ProjectAVR/minDUINO-v1.6-Eagle-/minDUINO v1.6_Gerblook_FRONT.jpg

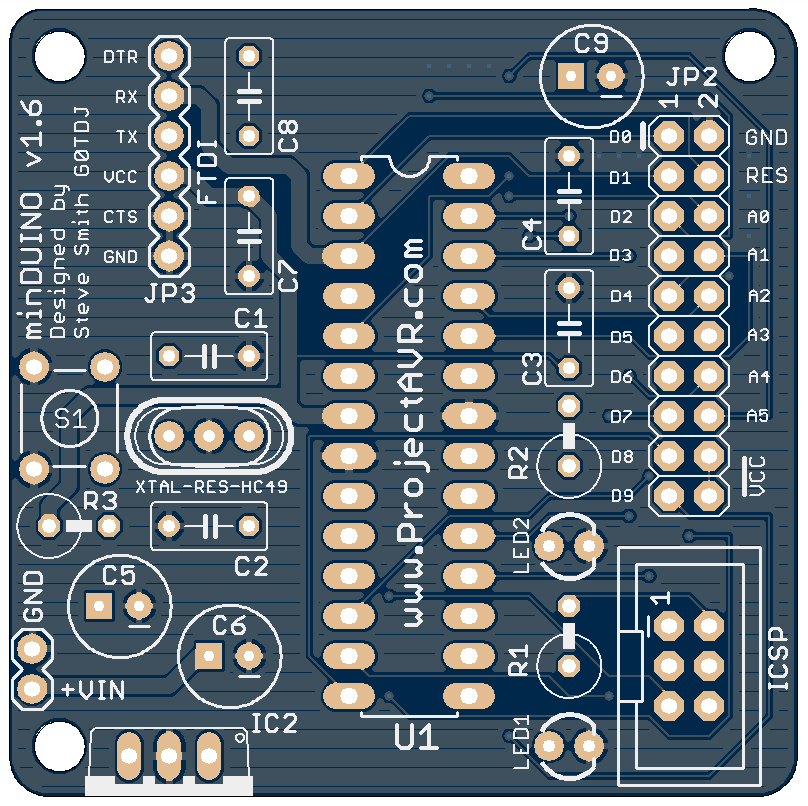
minDUINO v1.6_Gerblook_FRONT.jpg
