ProjectAVR/minDUINO-v1.6-Eagle-/MinDuino v1.6 Parts Placement.png

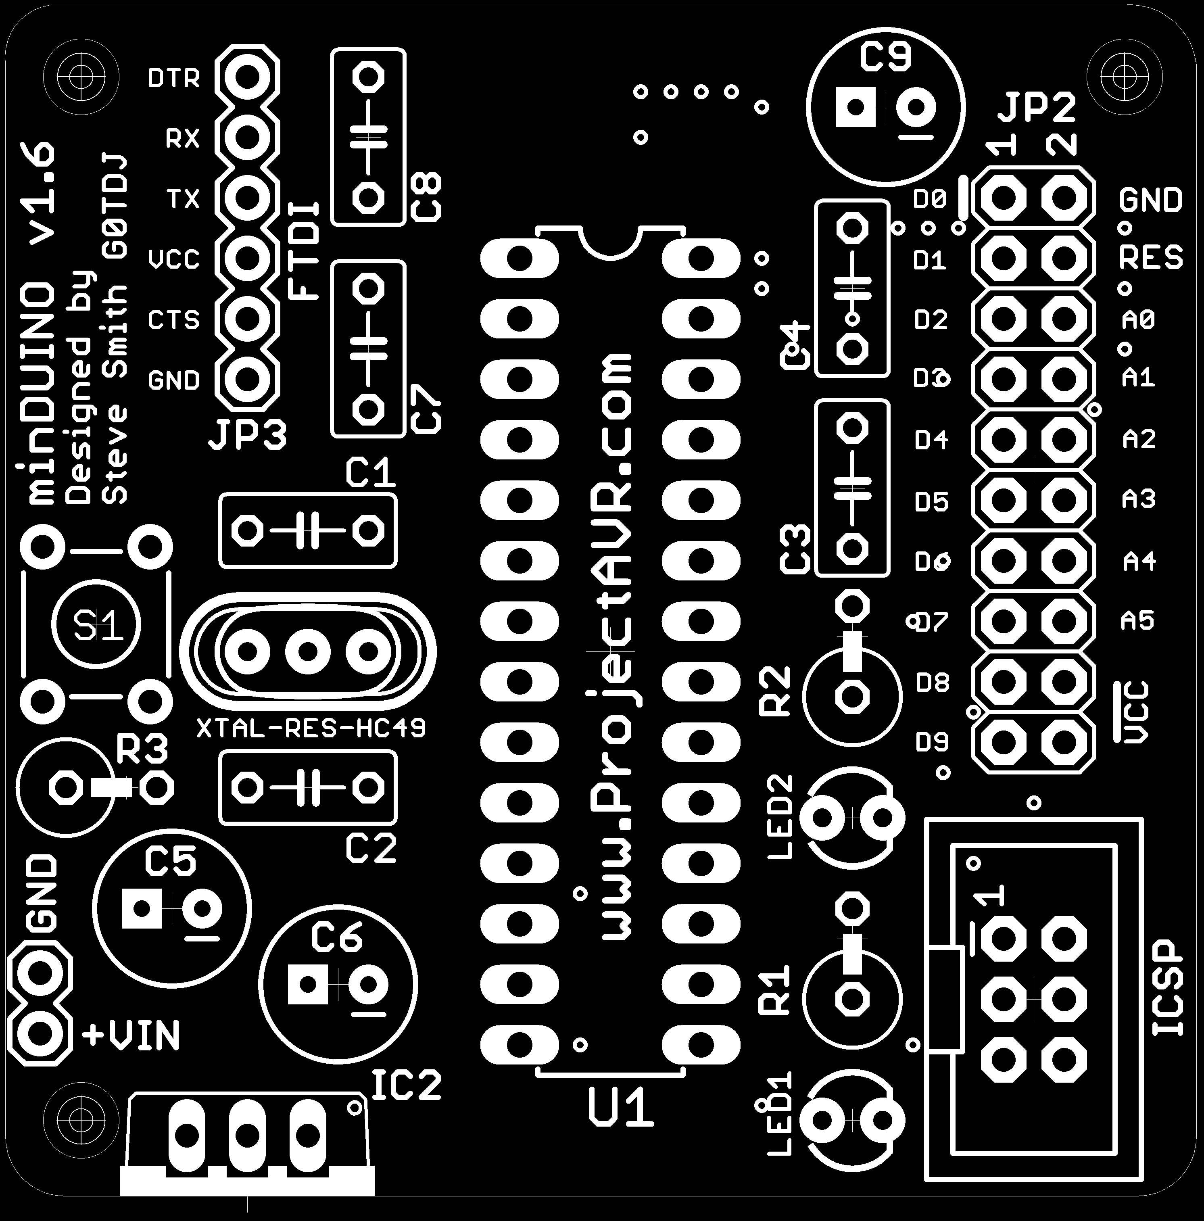
MinDuino v1.6 Parts Placement.png
